Isugar239/Artist/3D/dxf/задняя крыгка.dxf

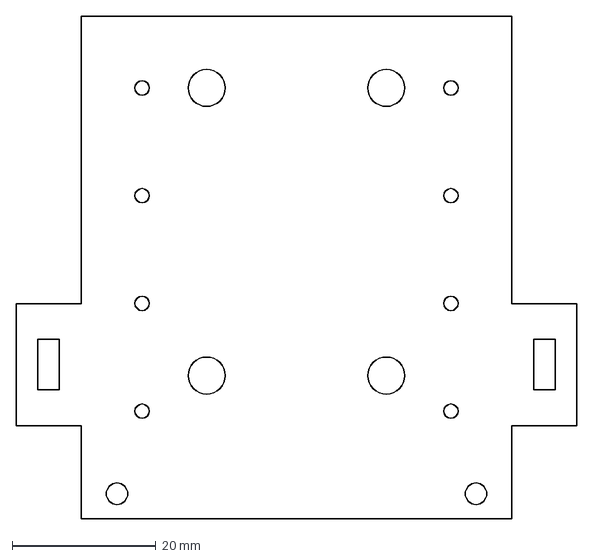
[picture p18: CAD file, 2026-01-08]
3D/dxf/задняя крыгка.dxf
78.0 x 70.0 mm
