Isugar239/Artist/3D/стл/крепеж_маркера.stp

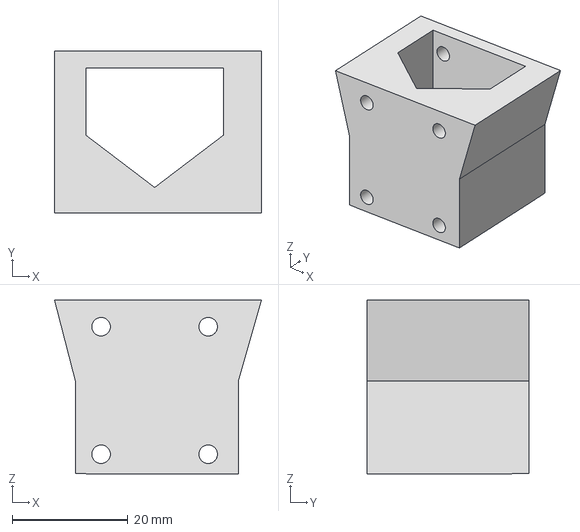
[picture p19: CAD file, 2026-01-11]
3D/стл/крепеж_маркера.stp
35.7 x 28.0 x 30.0 mm
