Isugar239/Artist/3D/dxf/baze_under.dxf

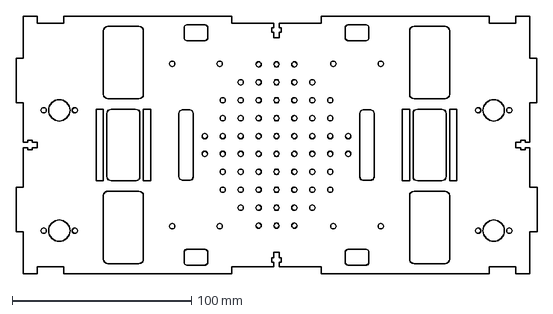
[picture p20: CAD file, 2026-01-08]
3D/dxf/baze_under.dxf
290.9 x 144.0 mm
