Isugar239/Artist/3D/стл/крепление тсрт.stp

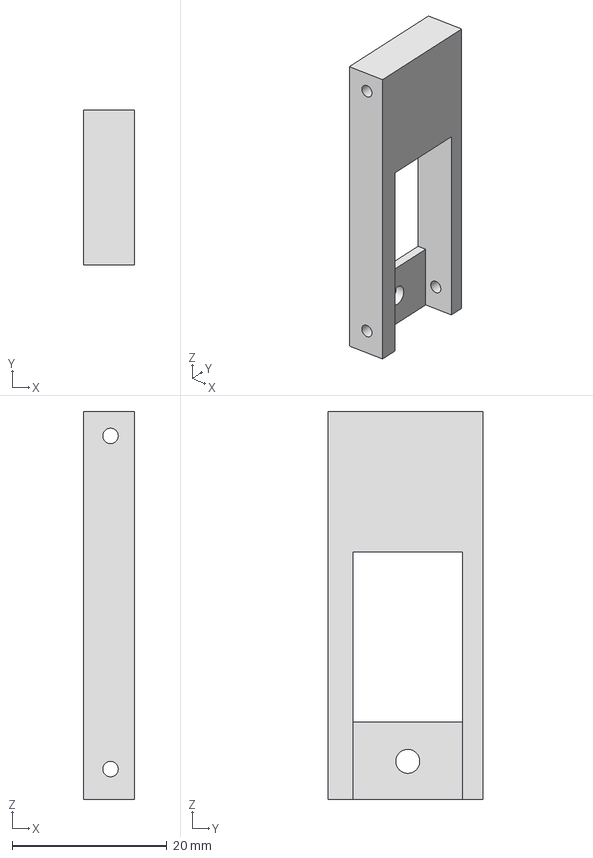
[picture p21: CAD file, 2026-01-11]
3D/стл/крепление тсрт.stp
6.56 x 20.0 x 50.2 mm
