Isugar239/Artist/3D/dxf/third_baze.dxf

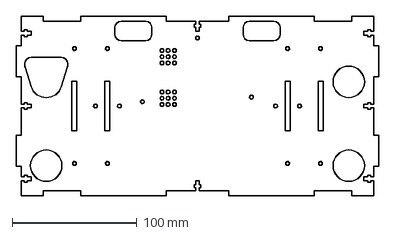
[picture p22: CAD file, 2026-01-08]
3D/dxf/third_baze.dxf
290.9 x 144.0 mm
