Isugar239/Artist/3D/стл/УГОЛОК.stp

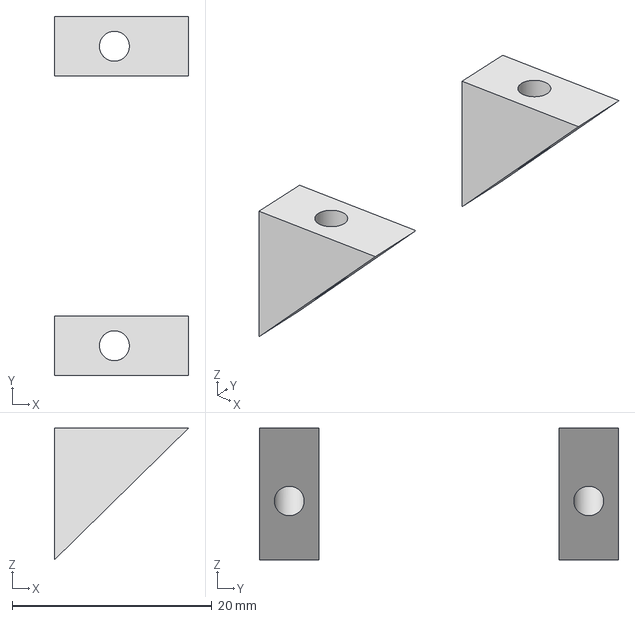
[picture p23: CAD file, 2026-01-11]
3D/стл/УГОЛОК.stp
13.4 x 36.0 x 13.2 mm
