Isugar239/Artist/3D/dxf/X2_down_balls.dxf

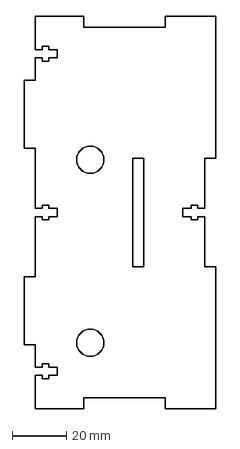
[picture p24: CAD file, 2026-01-08]
3D/dxf/X2_down_balls.dxf
70.2 x 144.0 mm
