Isugar239/Artist/3D/стл/4s.stp

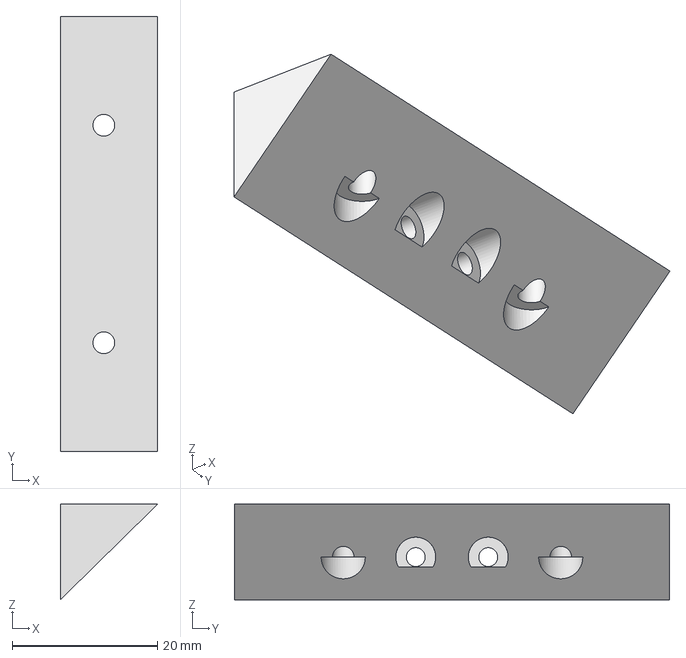
[picture p25: CAD file, 2026-01-11]
3D/стл/4s.stp
13.4 x 60.0 x 13.2 mm
