Isugar239/Artist/3D/dxf/X2_down_balls_mount1.dxf

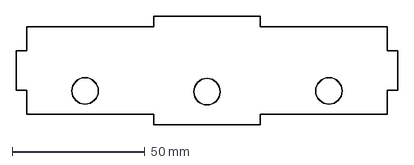
[picture p26: CAD file, 2026-01-08]
3D/dxf/X2_down_balls_mount1.dxf
144.0 x 41.0 mm
