Isugar239/Artist/3D/стл/крепление подшипника_1_CPY.stl

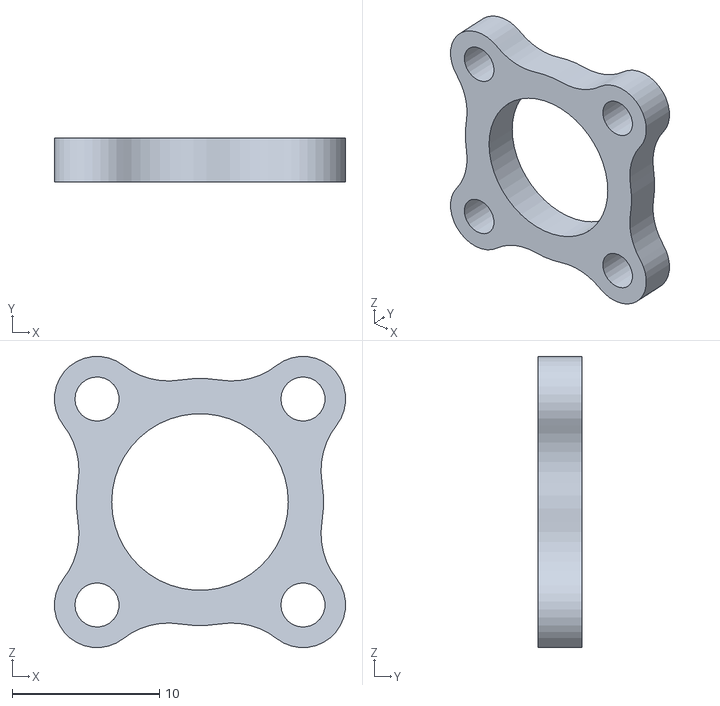
[picture p27: CAD file, 2026-01-08]
3D/стл/крепление подшипника_1_CPY.stl
19.8 x 3.00 x 19.8
