Isugar239/Artist/3D/dxf/передняя крышка.dxf

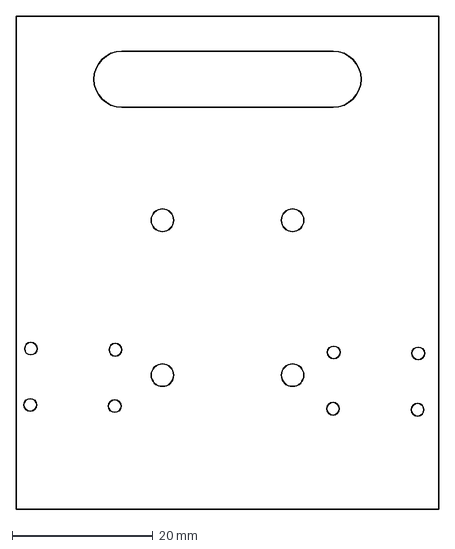
[picture p28: CAD file, 2026-01-08]
3D/dxf/передняя крышка.dxf
60.0 x 70.0 mm
