Isugar239/Artist/3D/стл/маркеркрепление маркера.stl

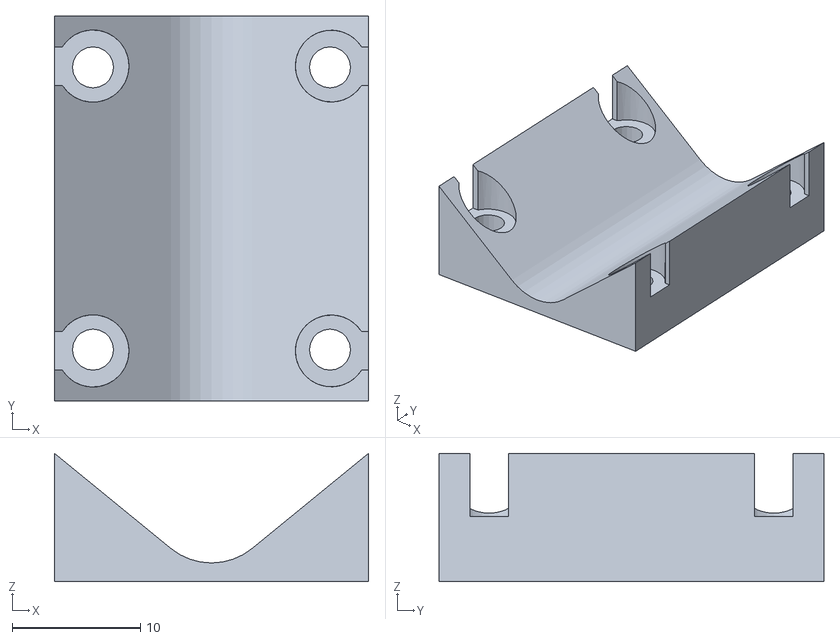
[picture p29: CAD file, 2026-01-08]
3D/стл/маркер крепление маркера.stl
24.5 x 30.0 x 10.0
