Isugar239/Artist/3D/dxf/under.dxf

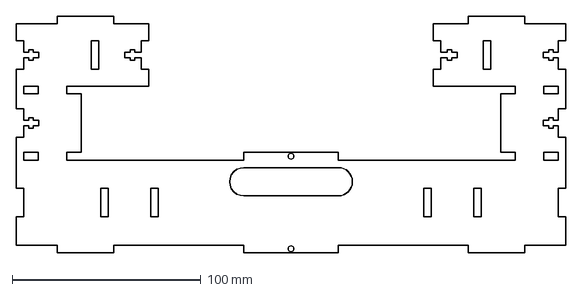
[picture p30: CAD file, 2026-01-08]
3D/dxf/under.dxf
290.9 x 125.0 mm
