Isugar239/Artist/3D/стл/Деталь2.stl

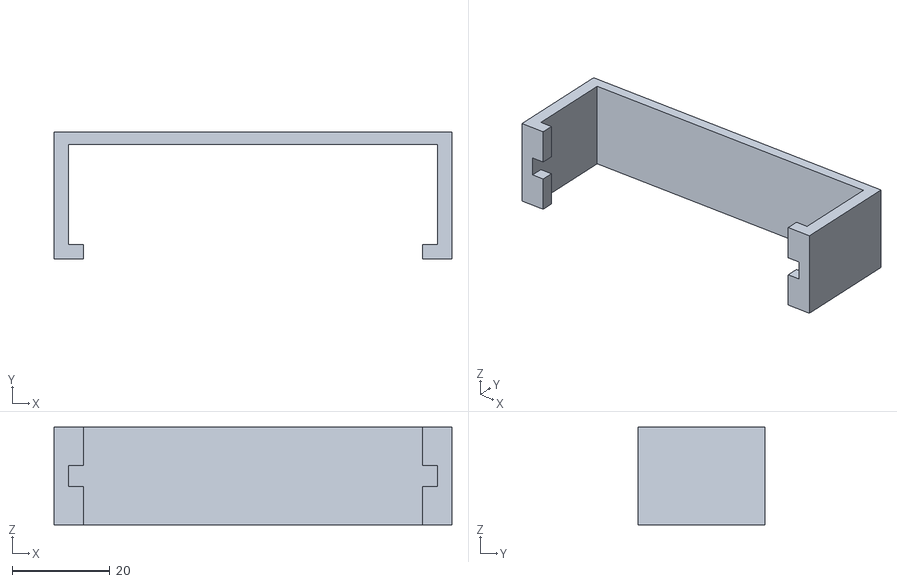
[picture p31: CAD file, 2026-01-08]
3D/стл/Деталь2.stl
81.5 x 26.0 x 20.0
