Isugar239/Artist/3D/dxf/низ_обновленный.dxf

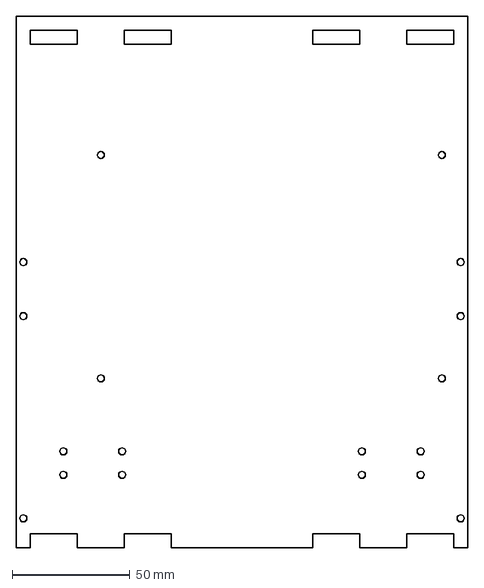
[picture p32: CAD file, 2026-01-07]
3D/dxf/низ_обновленный.dxf
192.0 x 226.0 mm
