Isugar239/Artist/3D/стл/ответка маркера.stl

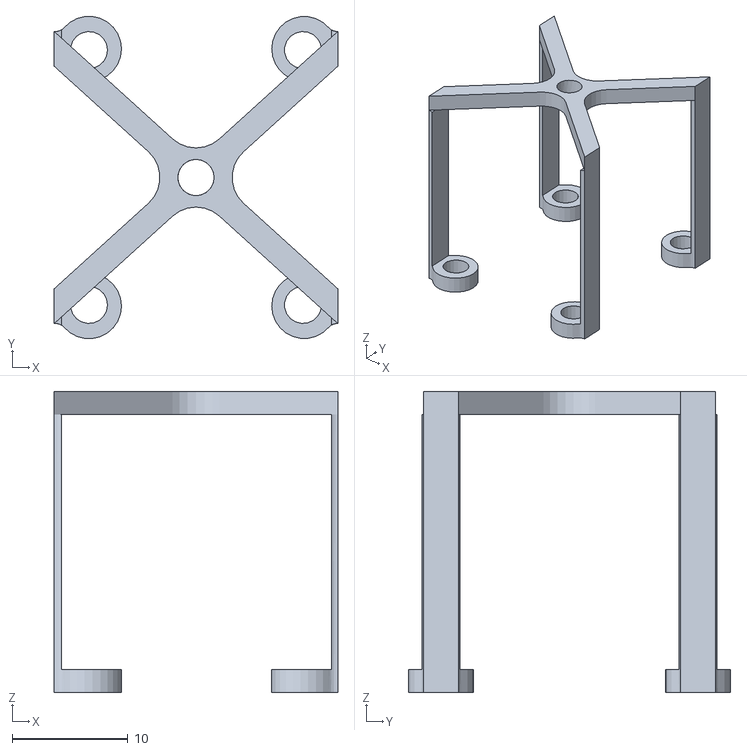
[picture p33: CAD file, 2026-01-08]
3D/стл/ответка маркера.stl
24.5 x 27.8 x 26.0
