Isugar239/Artist/3D/dxf/стенка с сервой.dxf

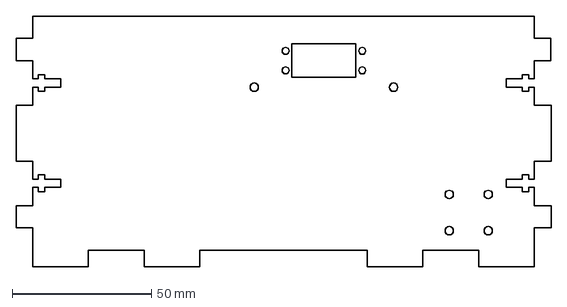
[picture p34: CAD file, 2025-12-08]
3D/dxf/стенка с сервой.dxf
192.0 x 90.0 mm
