Isugar239/Artist/3D/стл/крепление tcrt5000.stl

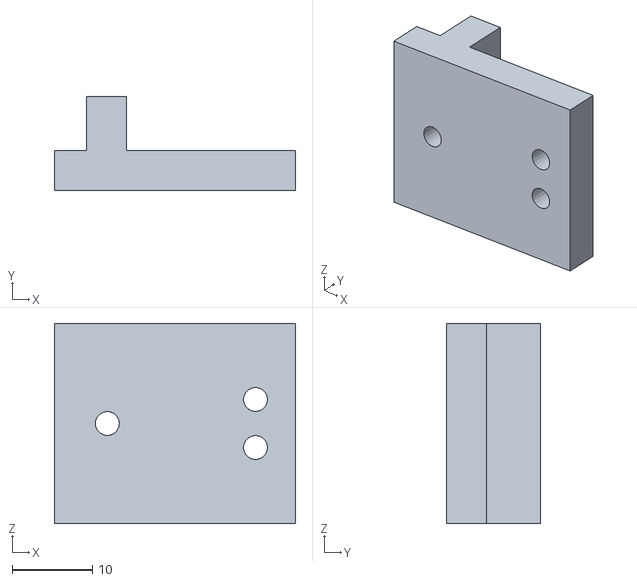
[picture p35: CAD file, 2026-01-08]
3D/стл/крепление tcrt5000.stl
30.1 x 11.7 x 25.0
