Isugar239/Artist/3D/dxf/боковая стенкк.dxf

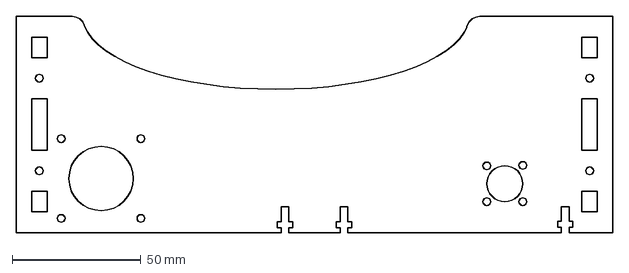
[picture p36: CAD file, 2025-12-08]
3D/dxf/боковая стенкк.dxf
232.0 x 84.0 mm
