Isugar239/Artist/3D/стл/соединялка.stl

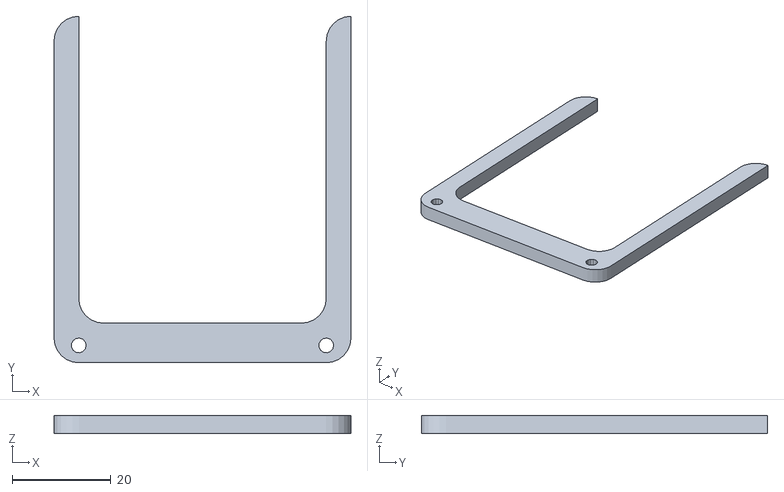
[picture p37: CAD file, 2026-01-08]
3D/стл/соединялка.stl
60.0 x 70.0 x 3.65
