Isugar239/Artist/3D/dxf/задняя стенка.dxf

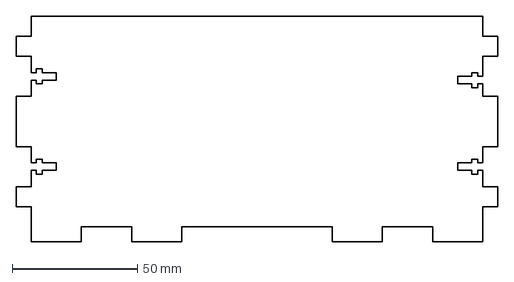
[picture p38: CAD file, 2025-12-08]
3D/dxf/задняя стенка.dxf
192.0 x 90.0 mm
