Isugar239/Artist/3D/стл/наименование.stl

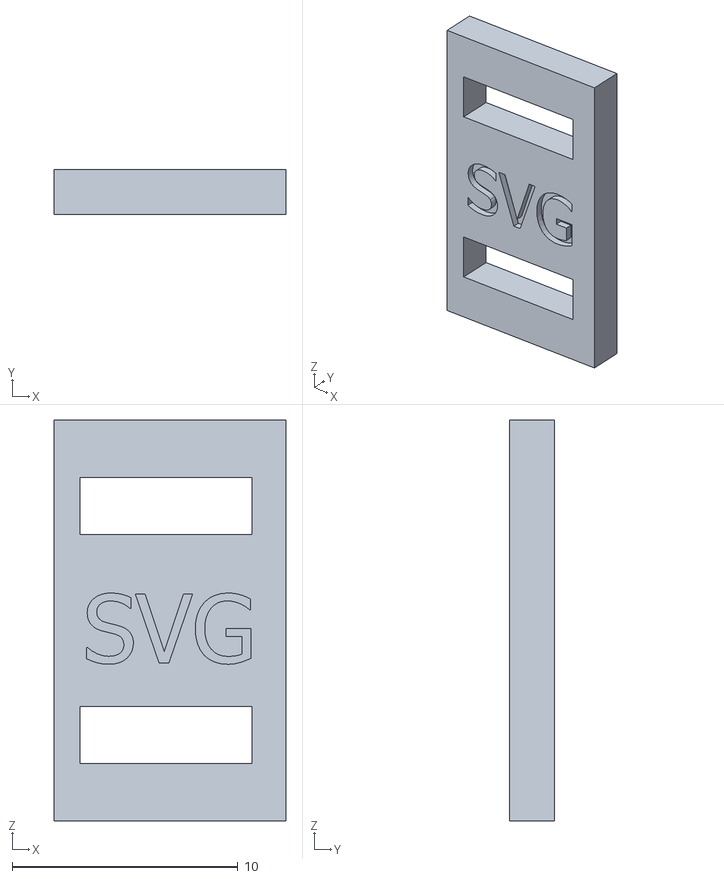
[picture p39: CAD file, 2026-01-07]
3D/стл/наименование.stl
10.3 x 2.00 x 17.8
