Isugar239/Artist/3D/dxf/низ.dxf

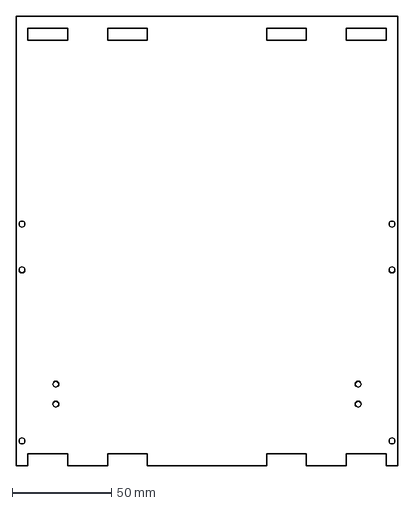
[picture p40: CAD file, 2025-12-08]
3D/dxf/низ.dxf
192.0 x 226.0 mm
