Isugar239/Artist/3D/стл/прослойка от батарей.stl

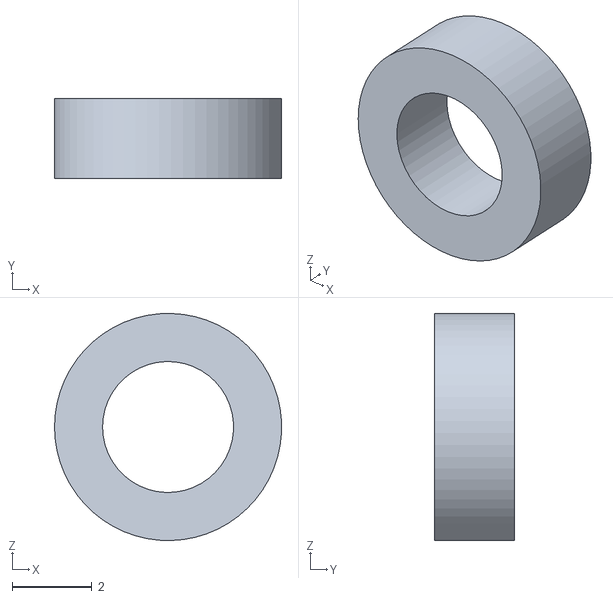
[picture p41: CAD file, 2026-01-07]
3D/стл/прослойка от батарей.stl
5.70 x 2.00 x 5.70
