Isugar239/Artist/3D/стл/Деталь1.stl

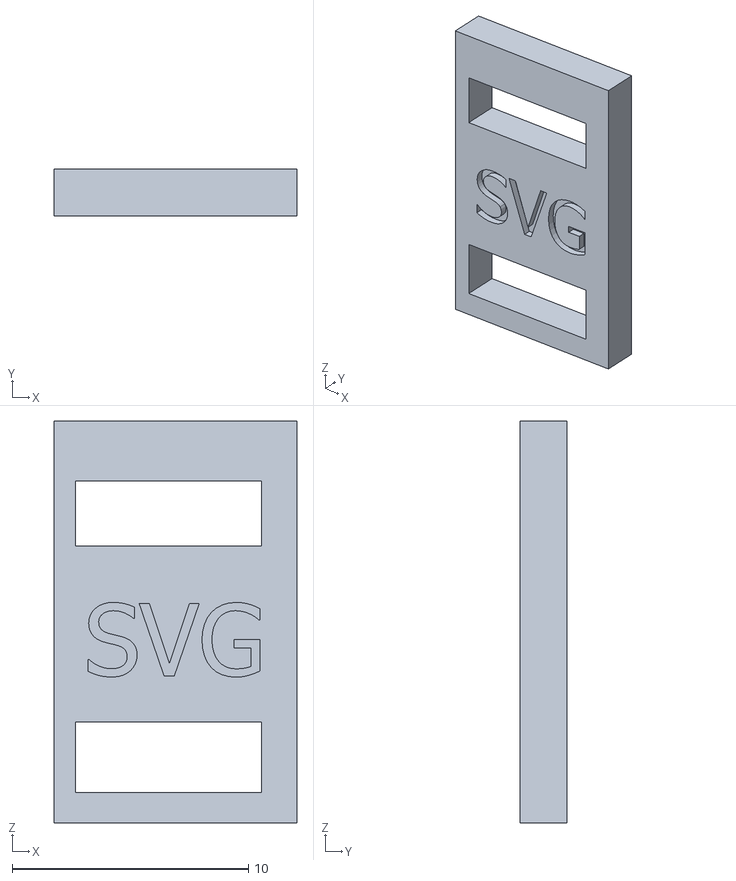
[picture p42: CAD file, 2026-01-07]
3D/стл/Деталь1.stl
10.3 x 2.00 x 17.0
