Isugar239/Artist/3D/стл/даржалка для камеры.stl

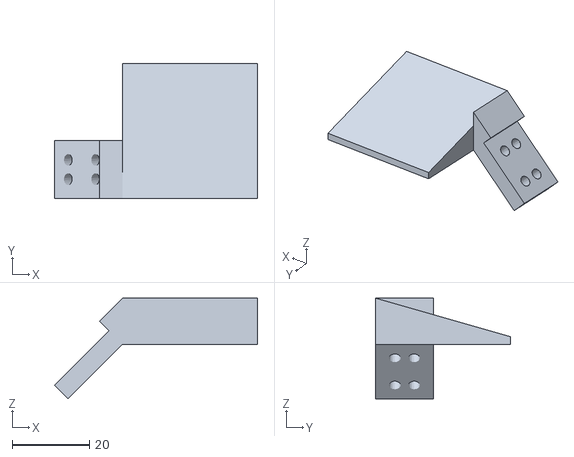
[picture p43: CAD file, 2025-12-30]
3D/стл/даржалка для камеры.stl
52.7 x 35.0 x 26.1
