Isugar239/Artist/3D/стл/деталь ек.stp

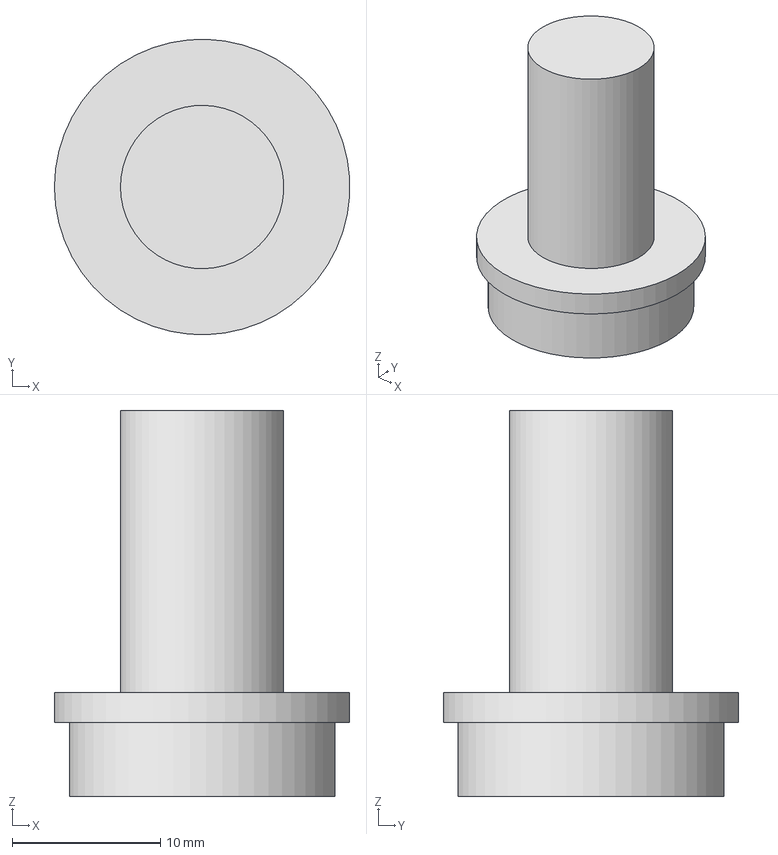
[picture p44: CAD file, 2025-12-30]
3D/стл/деталь ек.stp
19.9 x 19.9 x 26.0 mm
