Isugar239/Artist/3D/стл/робот-энкодер.stl

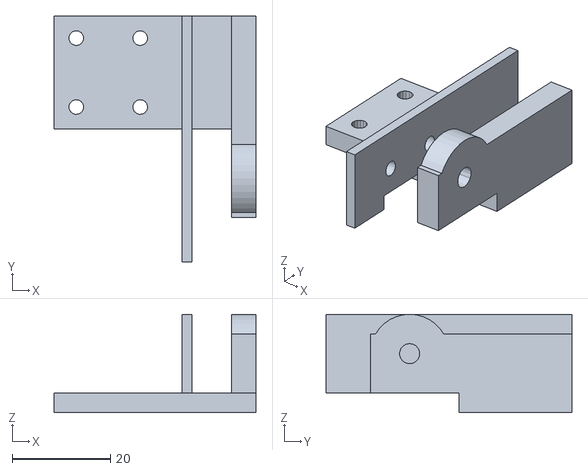
[picture p45: CAD file, 2025-12-30]
3D/стл/робот-энкодер.stl
41.0 x 50.0 x 20.0
