Isugar239/Artist/3D/стл/держалка для камеры.dxf

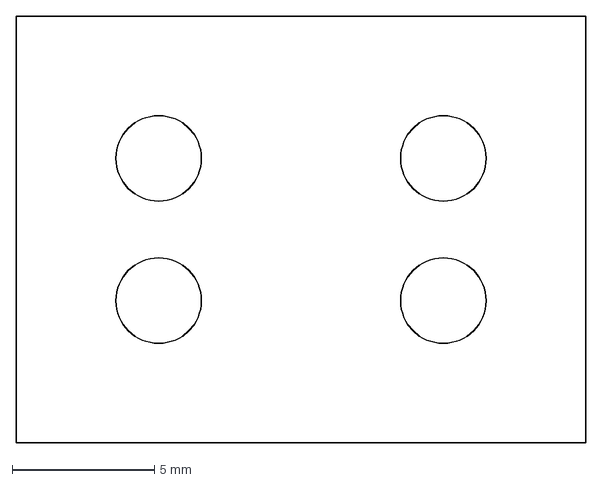
[picture p46: CAD file, 2025-12-30]
3D/стл/держалка для камеры.dxf
20.0 x 15.0 mm
