Isugar239/Artist/3D/стл/Муфта.stp

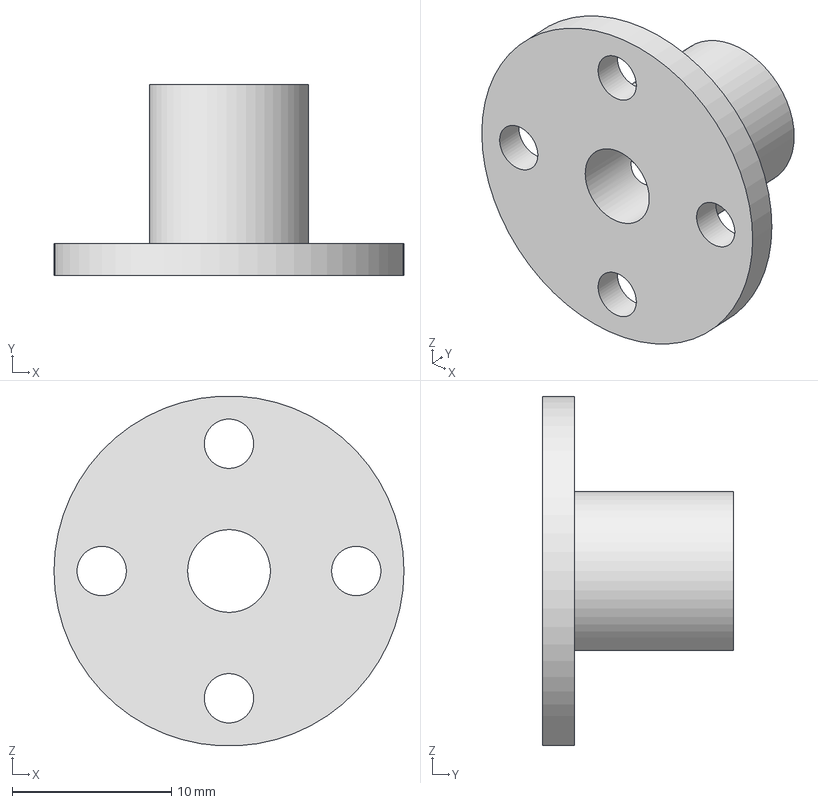
[picture p47: CAD file, 2025-12-30]
3D/стл/Муфта.stp
22.0 x 12.0 x 22.0 mm
