Isugar239/Artist/3D/стл/крепление подшипника_1.stp

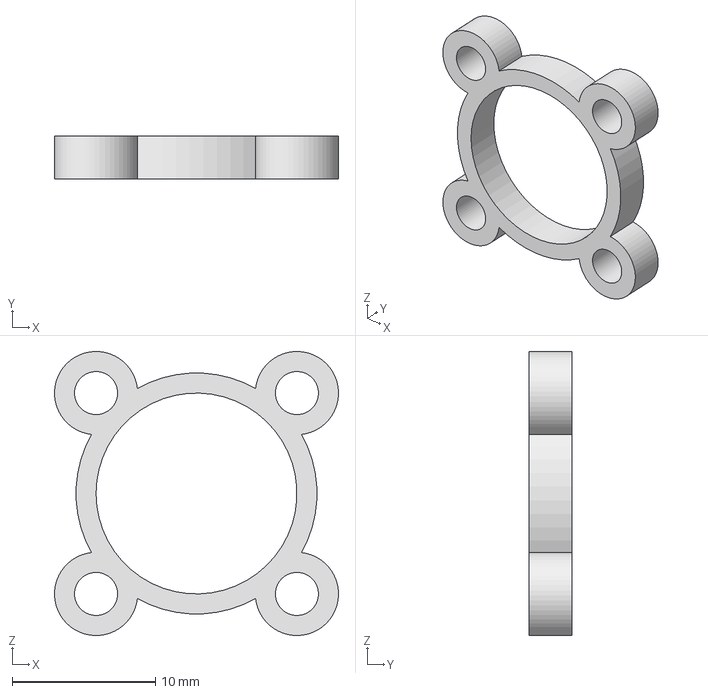
[picture p48: CAD file, 2025-12-30]
3D/стл/крепление подшипника_1.stp
19.8 x 3.00 x 19.8 mm
