Isugar239/Artist/3D/стл/держатель вала.stp

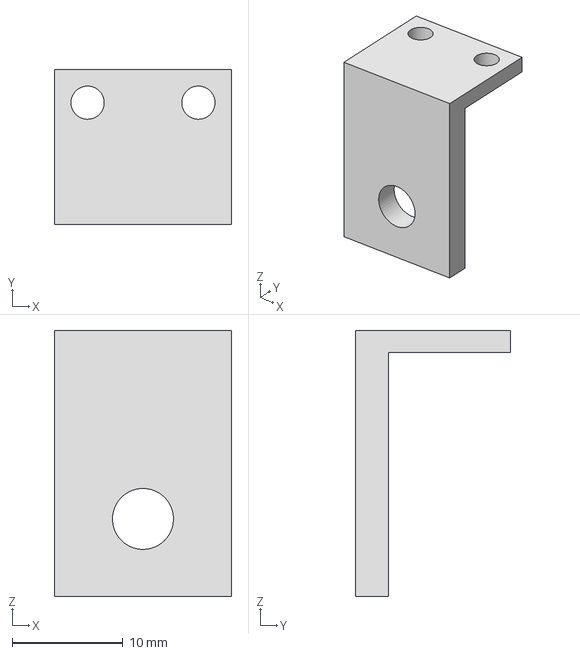
[picture p49: CAD file, 2025-12-30]
3D/стл/держатель вала.stp
16.0 x 14.0 x 24.0 mm
