Isugar239/Artist/3D/стл/k400+ полная.stl

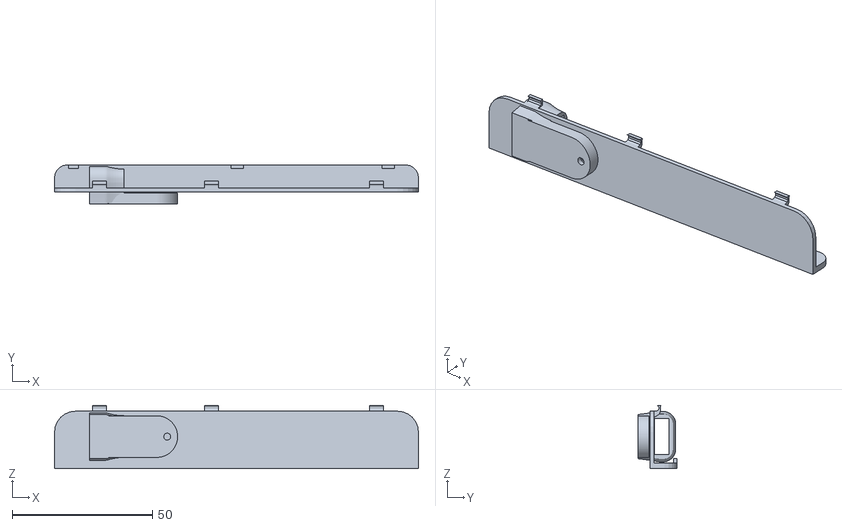
[picture p50: CAD file, 2025-12-08]
3D/стл/k400+ полная.stl
130.0 x 14.0 x 22.6
