Isugar239/Artist/3D/стл/k400+ крышка.stl

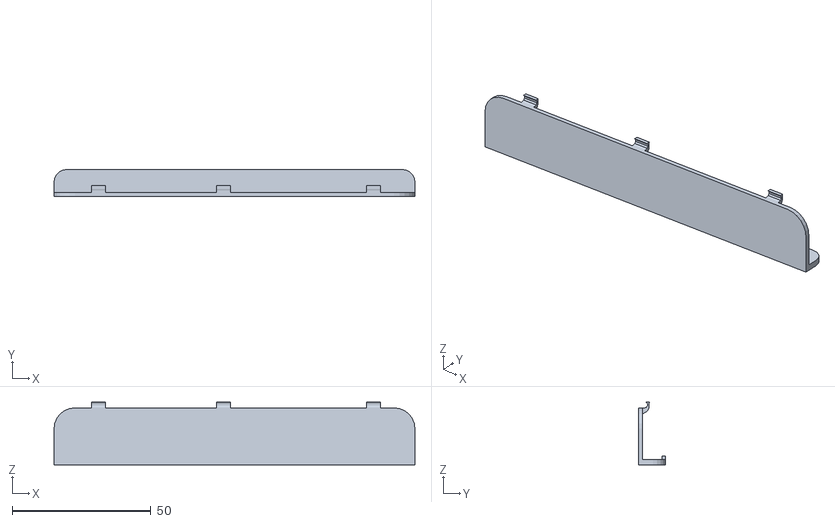
[picture p51: CAD file, 2025-12-06]
3D/стл/k400+ крышка.stl
130.0 x 9.70 x 22.6
