Isugar239/Artist/3D/стл/для резинки.stl

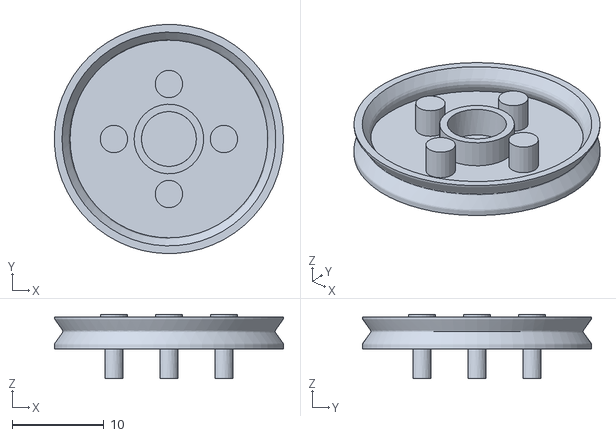
[picture p52: CAD file, 2025-12-06]
3D/стл/для резинки.stl
25.0 x 25.0 x 7.00
