Isugar239/Artist/3D/стл/крутящаяся передача.stl

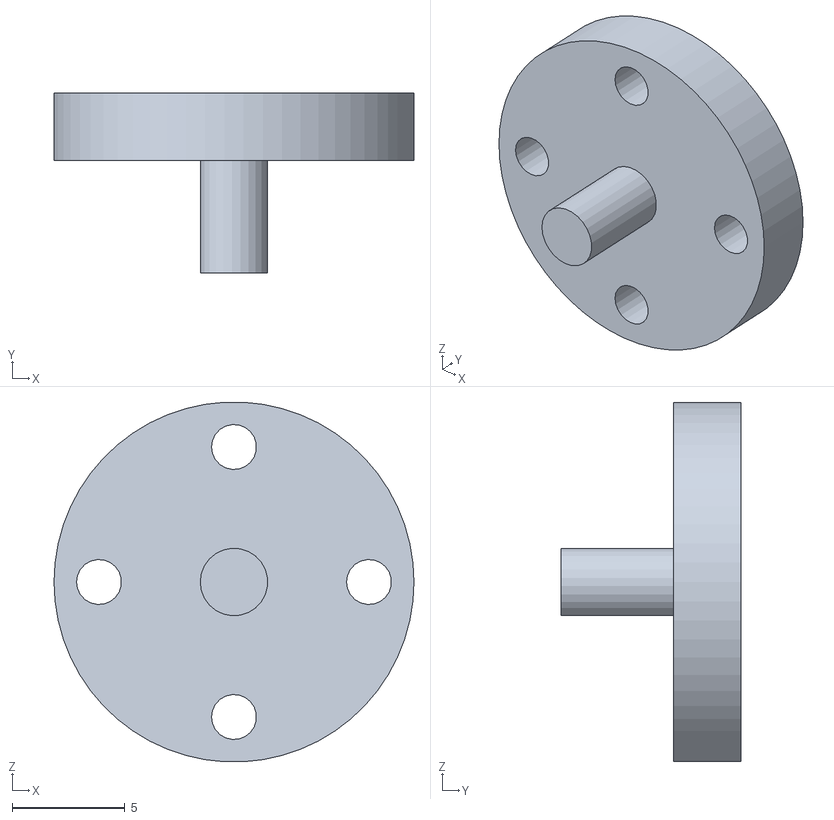
[picture p53: CAD file, 2025-12-06]
3D/стл/крутящаяся передача.stl
16.0 x 8.00 x 16.0
