Isugar239/Artist/3D/стл/clamp_m3_12mm.stl

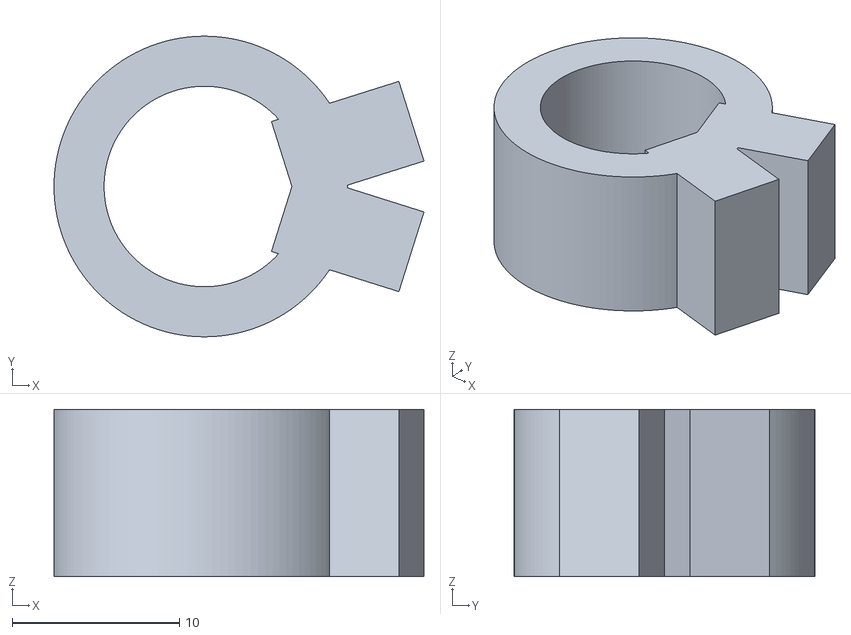
[picture p54: CAD file, 2025-12-01]
3D/стл/clamp_m3_12mm.stl
22.2 x 18.0 x 10.0
