Isugar239/Artist/3D/стл/Double Helix DNA.stl

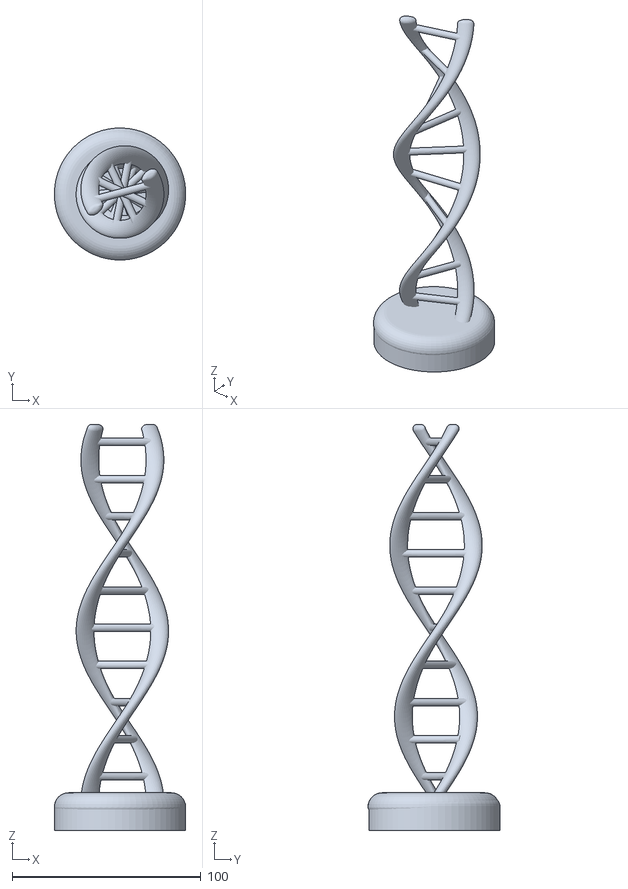
[picture p55: CAD file, 2025-12-01]
3D/стл/Double Helix DNA.stl
69.5 x 69.9 x 215.0
