Isugar239/Artist/3D/стл/Сборка плоттер.stp

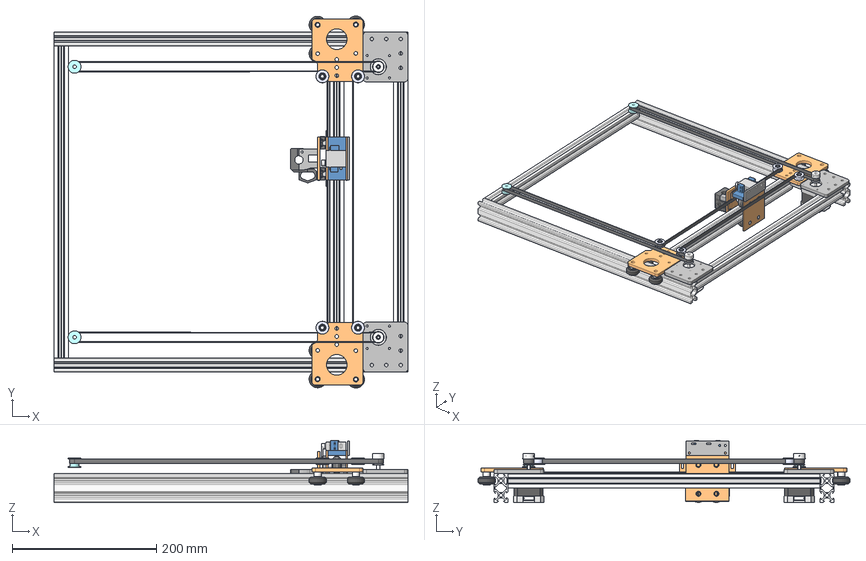
[picture p56: CAD file, 2025-12-01]
3D/стл/Сборка плоттер.stp
491.3 x 516.4 x 86.2 mm
2020 X x 2
NEMA17 Stepper x 2
2040 Y x 2
Крепление мотора x 2
Solid V-Wheel x 8
Ball Bearing 625 2RS 5x16x5 x 16
1mm 5mm shim x 16
Aluminium spacer 6mm x 8
A211 Высокоточная дистанционная шайба 5 мм x 4
A201 Дистанционная втулка 5х6 мм x 4
A195 Стандартный эксцентрик 6 мм, для винта М5 x 4
A181 Подшипник 625rs, O 5 O 16 x 8
A172 Стандартный пластиковый ролик для V-паза x 4
A137 Высокоточная прокладка O 5,3 O 8 x 8
MGN7 rail_100 mm x 2
MGN7C_MGN7C x 2
X Carriage
Ремень
GT2 drive wheel x 2
Smooth Pulley 10mm x 2
Body, GT2 Idler Pulley, Configurable_20T W6 B5 Without T x 4
Bearing Outer Ring, GT2 Idler Pulley, Configurable_5 mm Bore x 8
Bearing Inner Ring, GT2 Idler Pulley, Configurable_5 mm Bore x 8
Bearing Seal, GT2 Idler Pulley, Configurable_5 mm Bore x 16
Bearing Ball, GT2 Idler Pulley, Configurable_1.4 mm x 96
