Isugar239/Artist/3D/стл/NEMA17 42-40.stp

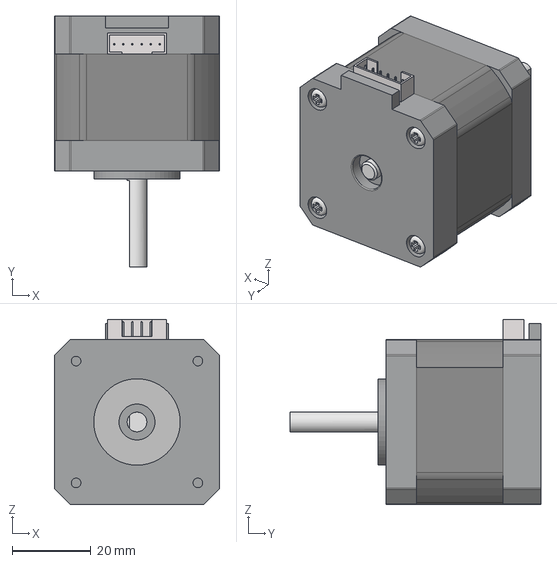
[picture p57: CAD file, 2025-12-01]
3D/стл/NEMA17 42-40.stp
42.0 x 63.8 x 47.1 mm
