Isugar239/Artist/3D/стл/abs_encider.stl

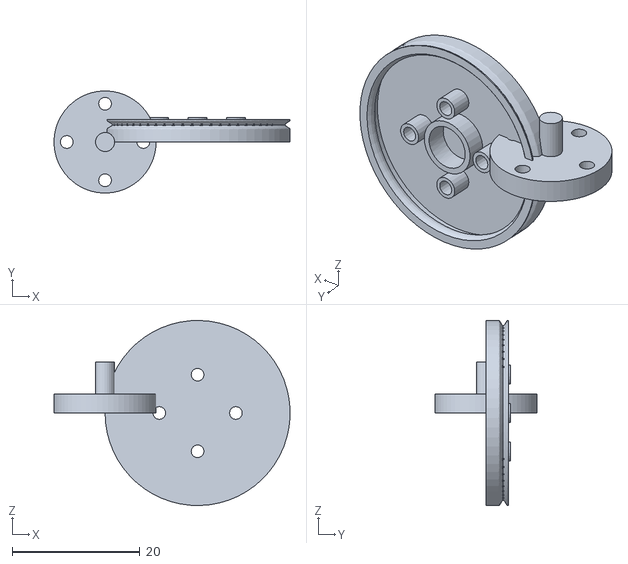
[picture p58: CAD file, 2025-11-27]
3D/стл/abs_encider.stl
37.0 x 16.0 x 29.0
