Isugar239/Artist/3D/стл/крепление подшипника_2.stl

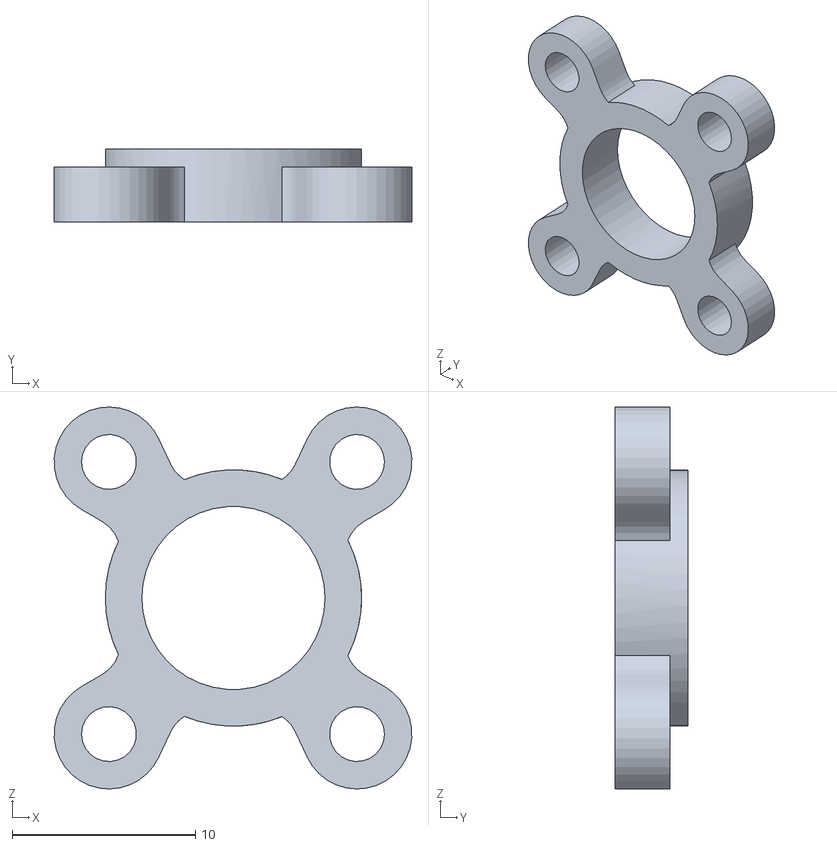
[picture p59: CAD file, 2025-11-25]
3D/стл/крепление подшипника_2.stl
19.5 x 4.00 x 20.9
