Isugar239/Artist/3D/стл/гран.dxf

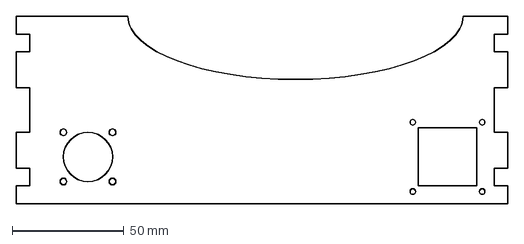
[picture p60: CAD file, 2025-11-25]
3D/стл/гран.dxf
220.0 x 84.0 mm
