Isugar239/Artist/3D/стл/Шест.stp

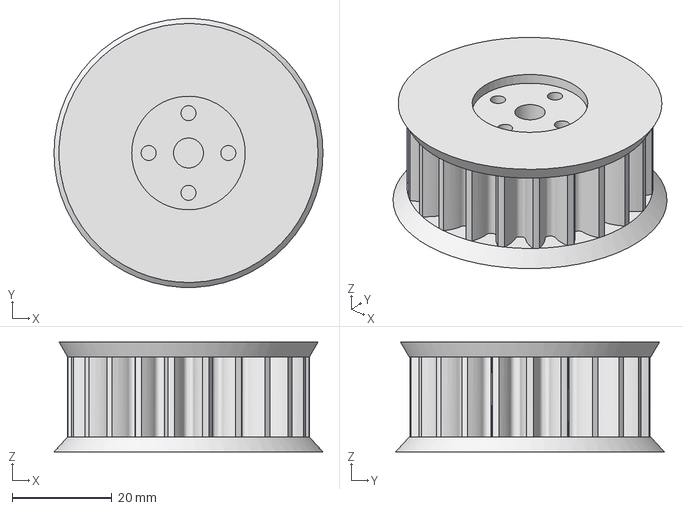
[picture p61: CAD file, 2025-11-24]
3D/стл/Шест.stp
54.0 x 53.9 x 22.0 mm
