Isugar239/Artist/3D/стл/Шестерня.stl

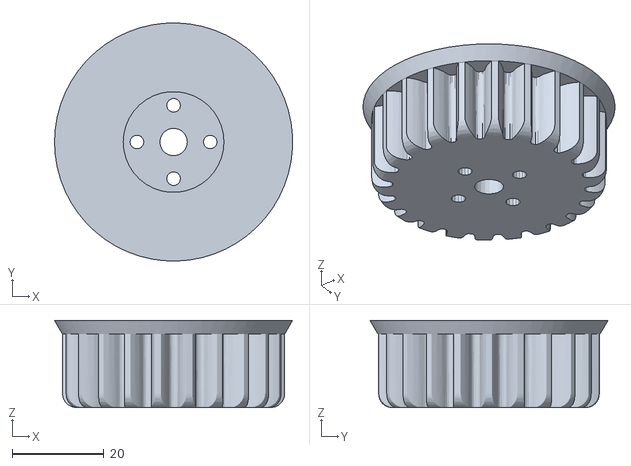
[picture p62: CAD file, 2025-11-22]
3D/стл/Шестерня.stl
52.0 x 52.0 x 19.0
